martinberlin/epdiy-hardware-versions/versions/v7-raw-34/3dmodels/FH34SRJ-8S-0.5SH_50.step

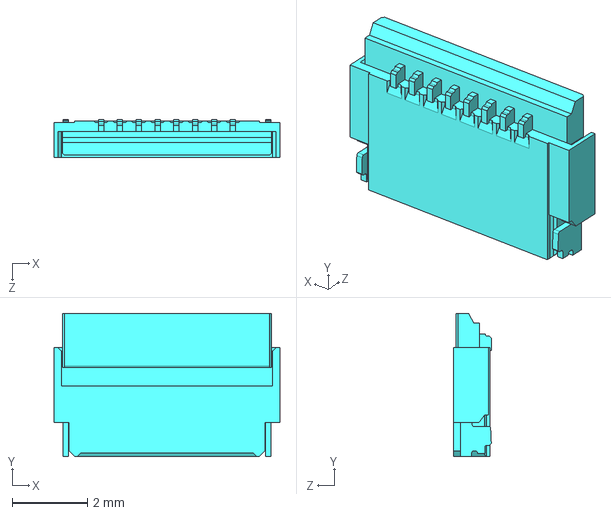
[picture p26: CAD file, 2025-05-24]
versions/v7-raw-34/3dmodels/FH34SRJ-8S-0.5SH_50.step
6.00 x 3.80 x 1.00 mm
