martinberlin/epdiy-hardware-versions/versions/v7-raw-34/kicad-libraries/3d/ESP32-S2-WROOM.STEP

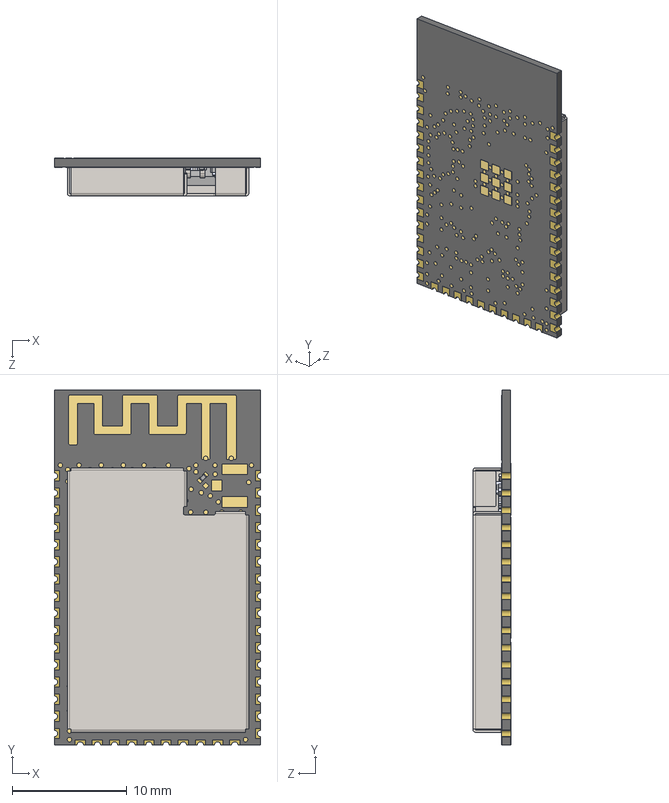
[picture p27: CAD file, 2025-05-24]
versions/v7-raw-34/kicad-libraries/3d/ESP32-S2-WROOM.STEP
18.0 x 31.0 x 3.30 mm
ESP32-S2_20210301.STEP^ESP32-S2_20210301.STEP_Submodel-QFN56_0P4_7_part_DesignRootModel_PCB_ESP32-S2-WROOM_V1(2)_PCB_ESP32-S2-WROOM_V1
R0201_20210301.STEP^R0201_20210301.STEP_Submodel-R0201_part_DesignRootModel_PCB_ESP32-S2-WROOM_V1(2)_PCB_ESP32-S2-WROOM_V1 x 7
trace_1^Submodel-MINI_ANT_TYPEB_1501846164_part_DesignRootModel_PCB_ESP32-S2-WROOM_V1(2)_PCB_ESP32-S2-WROOM_V1
C0201_20210301.STEP^C0201_20210301.STEP_Submodel-C0201_part_DesignRootModel_PCB_ESP32-S2-WROOM_V1(2)_PCB_ESP32-S2-WROOM_V1 x 15
DFN1006.STEP^DFN1006.STEP_Submodel-SOD882_part_DesignRootModel_PCB_ESP32-S2-WROOM_V1(2)_PCB_ESP32-S2-WROOM_V1
R0201_20210301.STEP^R0201_20210301.STEP_Submodel-R0201A_part_DesignRootModel_PCB_ESP32-S2-WROOM_V1(2)_PCB_ESP32-S2-WROOM_V1
L0201_20210301.STEP^L0201_20210301.STEP_Submodel-L0201_part_DesignRootModel_PCB_ESP32-S2-WROOM_V1(2)_PCB_ESP32-S2-WROOM_V1 x 2
C0402_20210301.STEP^C0402_20210301.STEP_Submodel-C0402_part_DesignRootModel_PCB_ESP32-S2-WROOM_V1(2)_PCB_ESP32-S2-WROOM_V1
XTAL3225_20210301.STEP^XTAL3225_20210301.STEP_Submodel-3225_part_DesignRootModel_PCB_ESP32-S2-WROOM_V1(2)_PCB_ESP32-S2-WROOM_V1
SOIC8_208_20210301.STEP^SOIC8_208_20210301.STEP_Submodel-SOIC08-WN_part_DesignRootModel_PCB_ESP32-S2-WROOM_V1(2)_PCB_ESP32-S2-WROOM_V1
uid__4-16^DesignRootModel_PCB_ESP32-S2-WROOM_V1(2)_PCB_ESP32-S2-WROOM_V1
uid__4-17^DesignRootModel_PCB_ESP32-S2-WROOM_V1(2)_PCB_ESP32-S2-WROOM_V1
uid__4-18^DesignRootModel_PCB_ESP32-S2-WROOM_V1(2)_PCB_ESP32-S2-WROOM_V1
uid__4-19^DesignRootModel_PCB_ESP32-S2-WROOM_V1(2)_PCB_ESP32-S2-WROOM_V1
uid__4-20^DesignRootModel_PCB_ESP32-S2-WROOM_V1(2)_PCB_ESP32-S2-WROOM_V1
uid__4-21^DesignRootModel_PCB_ESP32-S2-WROOM_V1(2)_PCB_ESP32-S2-WROOM_V1
uid__4-22^DesignRootModel_PCB_ESP32-S2-WROOM_V1(2)_PCB_ESP32-S2-WROOM_V1
uid__4-23^DesignRootModel_PCB_ESP32-S2-WROOM_V1(2)_PCB_ESP32-S2-WROOM_V1
uid__4-24^DesignRootModel_PCB_ESP32-S2-WROOM_V1(2)_PCB_ESP32-S2-WROOM_V1
uid__4-25^DesignRootModel_PCB_ESP32-S2-WROOM_V1(2)_PCB_ESP32-S2-WROOM_V1
uid__4-26^DesignRootModel_PCB_ESP32-S2-WROOM_V1(2)_PCB_ESP32-S2-WROOM_V1
uid__4-27^DesignRootModel_PCB_ESP32-S2-WROOM_V1(2)_PCB_ESP32-S2-WROOM_V1
uid__4-28^DesignRootModel_PCB_ESP32-S2-WROOM_V1(2)_PCB_ESP32-S2-WROOM_V1
uid__4-29^DesignRootModel_PCB_ESP32-S2-WROOM_V1(2)_PCB_ESP32-S2-WROOM_V1
uid__4-30^DesignRootModel_PCB_ESP32-S2-WROOM_V1(2)_PCB_ESP32-S2-WROOM_V1
uid__4-31^DesignRootModel_PCB_ESP32-S2-WROOM_V1(2)_PCB_ESP32-S2-WROOM_V1
uid__4-32^DesignRootModel_PCB_ESP32-S2-WROOM_V1(2)_PCB_ESP32-S2-WROOM_V1
uid__4-33^DesignRootModel_PCB_ESP32-S2-WROOM_V1(2)_PCB_ESP32-S2-WROOM_V1
uid__4-34^DesignRootModel_PCB_ESP32-S2-WROOM_V1(2)_PCB_ESP32-S2-WROOM_V1
uid__4-35^DesignRootModel_PCB_ESP32-S2-WROOM_V1(2)_PCB_ESP32-S2-WROOM_V1
uid__4-37^DesignRootModel_PCB_ESP32-S2-WROOM_V1(2)_PCB_ESP32-S2-WROOM_V1
uid__4-38^DesignRootModel_PCB_ESP32-S2-WROOM_V1(2)_PCB_ESP32-S2-WROOM_V1
uid__4-39^DesignRootModel_PCB_ESP32-S2-WROOM_V1(2)_PCB_ESP32-S2-WROOM_V1
uid__4-40^DesignRootModel_PCB_ESP32-S2-WROOM_V1(2)_PCB_ESP32-S2-WROOM_V1
uid__4-41^DesignRootModel_PCB_ESP32-S2-WROOM_V1(2)_PCB_ESP32-S2-WROOM_V1
uid__4-42^DesignRootModel_PCB_ESP32-S2-WROOM_V1(2)_PCB_ESP32-S2-WROOM_V1
uid__4-43^DesignRootModel_PCB_ESP32-S2-WROOM_V1(2)_PCB_ESP32-S2-WROOM_V1
uid__4-44^DesignRootModel_PCB_ESP32-S2-WROOM_V1(2)_PCB_ESP32-S2-WROOM_V1
uid__4-45^DesignRootModel_PCB_ESP32-S2-WROOM_V1(2)_PCB_ESP32-S2-WROOM_V1
uid__4-46^DesignRootModel_PCB_ESP32-S2-WROOM_V1(2)_PCB_ESP32-S2-WROOM_V1
uid__4-47^DesignRootModel_PCB_ESP32-S2-WROOM_V1(2)_PCB_ESP32-S2-WROOM_V1
uid__4-48^DesignRootModel_PCB_ESP32-S2-WROOM_V1(2)_PCB_ESP32-S2-WROOM_V1
uid__4-49^DesignRootModel_PCB_ESP32-S2-WROOM_V1(2)_PCB_ESP32-S2-WROOM_V1
uid__4-50^DesignRootModel_PCB_ESP32-S2-WROOM_V1(2)_PCB_ESP32-S2-WROOM_V1
uid__4-51^DesignRootModel_PCB_ESP32-S2-WROOM_V1(2)_PCB_ESP32-S2-WROOM_V1
uid__4-52^DesignRootModel_PCB_ESP32-S2-WROOM_V1(2)_PCB_ESP32-S2-WROOM_V1
uid__4-53^DesignRootModel_PCB_ESP32-S2-WROOM_V1(2)_PCB_ESP32-S2-WROOM_V1
uid__4-54^DesignRootModel_PCB_ESP32-S2-WROOM_V1(2)_PCB_ESP32-S2-WROOM_V1
uid__4-56^DesignRootModel_PCB_ESP32-S2-WROOM_V1(2)_PCB_ESP32-S2-WROOM_V1
uid__4-57^DesignRootModel_PCB_ESP32-S2-WROOM_V1(2)_PCB_ESP32-S2-WROOM_V1
uid__4-58^DesignRootModel_PCB_ESP32-S2-WROOM_V1(2)_PCB_ESP32-S2-WROOM_V1
uid__4-59^DesignRootModel_PCB_ESP32-S2-WROOM_V1(2)_PCB_ESP32-S2-WROOM_V1
uid__4-60^DesignRootModel_PCB_ESP32-S2-WROOM_V1(2)_PCB_ESP32-S2-WROOM_V1
uid__4-61^DesignRootModel_PCB_ESP32-S2-WROOM_V1(2)_PCB_ESP32-S2-WROOM_V1
uid__4-62^DesignRootModel_PCB_ESP32-S2-WROOM_V1(2)_PCB_ESP32-S2-WROOM_V1
uid__4-63^DesignRootModel_PCB_ESP32-S2-WROOM_V1(2)_PCB_ESP32-S2-WROOM_V1
uid__4-64^DesignRootModel_PCB_ESP32-S2-WROOM_V1(2)_PCB_ESP32-S2-WROOM_V1
uid__4-65^DesignRootModel_PCB_ESP32-S2-WROOM_V1(2)_PCB_ESP32-S2-WROOM_V1
uid__4-66^DesignRootModel_PCB_ESP32-S2-WROOM_V1(2)_PCB_ESP32-S2-WROOM_V1
uid__4-67^DesignRootModel_PCB_ESP32-S2-WROOM_V1(2)_PCB_ESP32-S2-WROOM_V1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
