martinberlin/epdiy-hardware-versions/versions/v7-raw-34/3dmodels/THD2528-11SD-GF_microSD.step

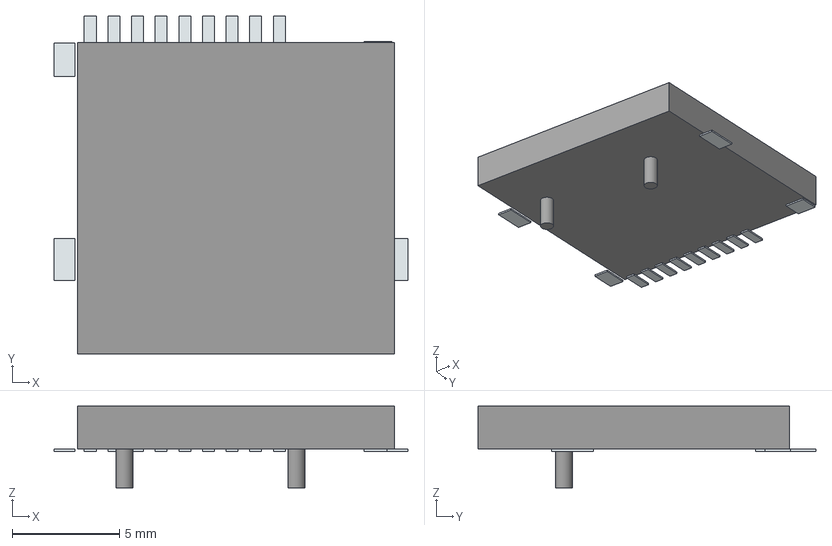
[picture p28: CAD file, 2025-05-24]
versions/v7-raw-34/3dmodels/THD2528-11SD-GF_microSD.step
16.5 x 15.7 x 3.80 mm
Pins
Lugs x 2
