martinberlin/epdiy-hardware-versions/versions/v7-raw-34/3dmodels/FH34SRJ-6S-0.5SH_99.step

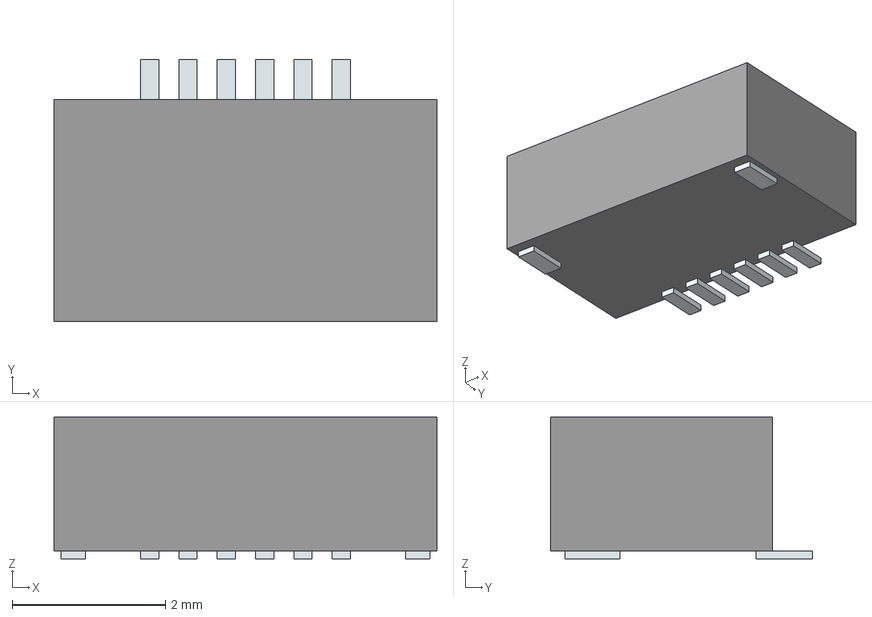
[picture p30: CAD file, 2025-05-24]
versions/v7-raw-34/3dmodels/FH34SRJ-6S-0.5SH_99.step
5.00 x 3.42 x 1.85 mm
Pins
