martinberlin/epdiy-hardware-versions/versions/v7-raw-34/kicad-libraries/3d/ESP32-S3-WROOM-1U.STEP

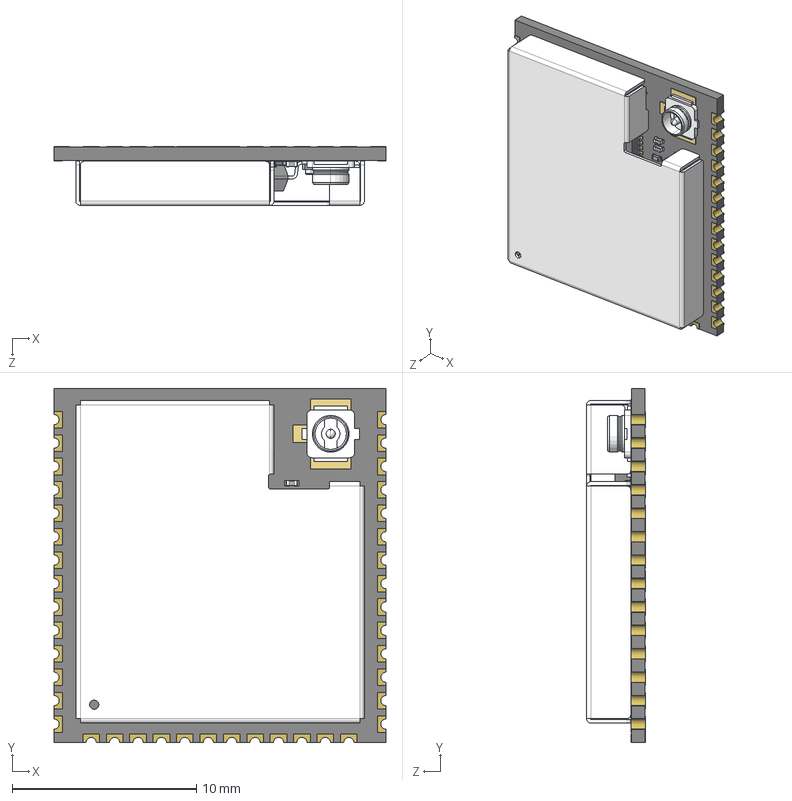
[picture p31: CAD file, 2025-05-24]
versions/v7-raw-34/kicad-libraries/3d/ESP32-S3-WROOM-1U.STEP
18.0 x 19.2 x 3.20 mm
R0201_20210301.STEP^R0201_20210301.STEP_Submodel-R0201_part_DesignRootModel_ESP32-S3-WROOM-1U(2)_ESP32-S3-WROOM-1U x 8
L0201_20210301.STEP^L0201_20210301.STEP_Submodel-L0201_part_DesignRootModel_ESP32-S3-WROOM-1U(2)_ESP32-S3-WROOM-1U x 2
C0201_20210301.STEP^C0201_20210301.STEP_Submodel-C0201_part_DesignRootModel_ESP32-S3-WROOM-1U(2)_ESP32-S3-WROOM-1U x 13
C0402_20210301.STEP^C0402_20210301.STEP_Submodel-C0402_part_DesignRootModel_ESP32-S3-WROOM-1U(2)_ESP32-S3-WROOM-1U
I-IPEX.STEP^I-IPEX.STEP_Submodel-IPEX_3P_part_DesignRootModel_ESP32-S3-WROOM-1U(2)_ESP32-S3-WROOM-1U
DFN1006.STEP^DFN1006.STEP_Submodel-SOD882_part_DesignRootModel_ESP32-S3-WROOM-1U(2)_ESP32-S3-WROOM-1U
SOP8_rev1_20210308.STEP^SOP8_rev1_20210308.STEP_Submodel-SOP8_1P27_6P6_part_DesignRootModel_ESP32-S3-WROOM-1U(2)_ESP32-S3-WROOM-1U
ESP32-S3_20210301.STEP^ESP32-S3_20210301.STEP_Submodel-QFN56_0P4_7_part_DesignRootModel_ESP32-S3-WROOM-1U(2)_ESP32-S3-WROOM-1U
XTAL3225_20210301.STEP^XTAL3225_20210301.STEP_Submodel-XTAL3225_part_DesignRootModel_ESP32-S3-WROOM-1U(2)_ESP32-S3-WROOM-1U
uid__4-111^DesignRootModel_ESP32-S3-WROOM-1U(2)_ESP32-S3-WROOM-1U
uid__4-112^DesignRootModel_ESP32-S3-WROOM-1U(2)_ESP32-S3-WROOM-1U
uid__4-113^DesignRootModel_ESP32-S3-WROOM-1U(2)_ESP32-S3-WROOM-1U
uid__4-130^DesignRootModel_ESP32-S3-WROOM-1U(2)_ESP32-S3-WROOM-1U
uid__4-131^DesignRootModel_ESP32-S3-WROOM-1U(2)_ESP32-S3-WROOM-1U
uid__4-132^DesignRootModel_ESP32-S3-WROOM-1U(2)_ESP32-S3-WROOM-1U
uid__4-148^DesignRootModel_ESP32-S3-WROOM-1U(2)_ESP32-S3-WROOM-1U
uid__4-149^DesignRootModel_ESP32-S3-WROOM-1U(2)_ESP32-S3-WROOM-1U
uid__4-150^DesignRootModel_ESP32-S3-WROOM-1U(2)_ESP32-S3-WROOM-1U
uid__1-253^DesignRootModel_ESP32-S3-WROOM-1U(2)_ESP32-S3-WROOM-1U
uid__1-254^DesignRootModel_ESP32-S3-WROOM-1U(2)_ESP32-S3-WROOM-1U
uid__1-256^DesignRootModel_ESP32-S3-WROOM-1U(2)_ESP32-S3-WROOM-1U
uid__1-257^DesignRootModel_ESP32-S3-WROOM-1U(2)_ESP32-S3-WROOM-1U
uid__1-266^DesignRootModel_ESP32-S3-WROOM-1U(2)_ESP32-S3-WROOM-1U
uid__1-269^DesignRootModel_ESP32-S3-WROOM-1U(2)_ESP32-S3-WROOM-1U
uid__1-270^DesignRootModel_ESP32-S3-WROOM-1U(2)_ESP32-S3-WROOM-1U
uid__1-271^DesignRootModel_ESP32-S3-WROOM-1U(2)_ESP32-S3-WROOM-1U
uid__1-272^DesignRootModel_ESP32-S3-WROOM-1U(2)_ESP32-S3-WROOM-1U
uid__1-273^DesignRootModel_ESP32-S3-WROOM-1U(2)_ESP32-S3-WROOM-1U
uid__1-274^DesignRootModel_ESP32-S3-WROOM-1U(2)_ESP32-S3-WROOM-1U
uid__1-275^DesignRootModel_ESP32-S3-WROOM-1U(2)_ESP32-S3-WROOM-1U
uid__1-276^DesignRootModel_ESP32-S3-WROOM-1U(2)_ESP32-S3-WROOM-1U
uid__1-277^DesignRootModel_ESP32-S3-WROOM-1U(2)_ESP32-S3-WROOM-1U
uid__1-280^DesignRootModel_ESP32-S3-WROOM-1U(2)_ESP32-S3-WROOM-1U
uid__1-292^DesignRootModel_ESP32-S3-WROOM-1U(2)_ESP32-S3-WROOM-1U
uid__1-293^DesignRootModel_ESP32-S3-WROOM-1U(2)_ESP32-S3-WROOM-1U
uid__1-297^DesignRootModel_ESP32-S3-WROOM-1U(2)_ESP32-S3-WROOM-1U
uid__1-300^DesignRootModel_ESP32-S3-WROOM-1U(2)_ESP32-S3-WROOM-1U
uid__1-301^DesignRootModel_ESP32-S3-WROOM-1U(2)_ESP32-S3-WROOM-1U
uid__1-302^DesignRootModel_ESP32-S3-WROOM-1U(2)_ESP32-S3-WROOM-1U
uid__1-303^DesignRootModel_ESP32-S3-WROOM-1U(2)_ESP32-S3-WROOM-1U
uid__1-307^DesignRootModel_ESP32-S3-WROOM-1U(2)_ESP32-S3-WROOM-1U
uid__1-313^DesignRootModel_ESP32-S3-WROOM-1U(2)_ESP32-S3-WROOM-1U
uid__1-319^DesignRootModel_ESP32-S3-WROOM-1U(2)_ESP32-S3-WROOM-1U
uid__1-320^DesignRootModel_ESP32-S3-WROOM-1U(2)_ESP32-S3-WROOM-1U
uid__1-321^DesignRootModel_ESP32-S3-WROOM-1U(2)_ESP32-S3-WROOM-1U
uid__1-328^DesignRootModel_ESP32-S3-WROOM-1U(2)_ESP32-S3-WROOM-1U
uid__1-332^DesignRootModel_ESP32-S3-WROOM-1U(2)_ESP32-S3-WROOM-1U
uid__1-333^DesignRootModel_ESP32-S3-WROOM-1U(2)_ESP32-S3-WROOM-1U
uid__1-334^DesignRootModel_ESP32-S3-WROOM-1U(2)_ESP32-S3-WROOM-1U
uid__1-335^DesignRootModel_ESP32-S3-WROOM-1U(2)_ESP32-S3-WROOM-1U
uid__1-336^DesignRootModel_ESP32-S3-WROOM-1U(2)_ESP32-S3-WROOM-1U
uid__1-337^DesignRootModel_ESP32-S3-WROOM-1U(2)_ESP32-S3-WROOM-1U
uid__1-338^DesignRootModel_ESP32-S3-WROOM-1U(2)_ESP32-S3-WROOM-1U
uid__1-339^DesignRootModel_ESP32-S3-WROOM-1U(2)_ESP32-S3-WROOM-1U
uid__1-340^DesignRootModel_ESP32-S3-WROOM-1U(2)_ESP32-S3-WROOM-1U
uid__1-341^DesignRootModel_ESP32-S3-WROOM-1U(2)_ESP32-S3-WROOM-1U
uid__1-342^DesignRootModel_ESP32-S3-WROOM-1U(2)_ESP32-S3-WROOM-1U
uid__1-343^DesignRootModel_ESP32-S3-WROOM-1U(2)_ESP32-S3-WROOM-1U
uid__1-344^DesignRootModel_ESP32-S3-WROOM-1U(2)_ESP32-S3-WROOM-1U
uid__1-345^DesignRootModel_ESP32-S3-WROOM-1U(2)_ESP32-S3-WROOM-1U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
