martinberlin/epdiy-hardware-versions/versions/v7-raw-34/3dmodels/L-40xx.STEP

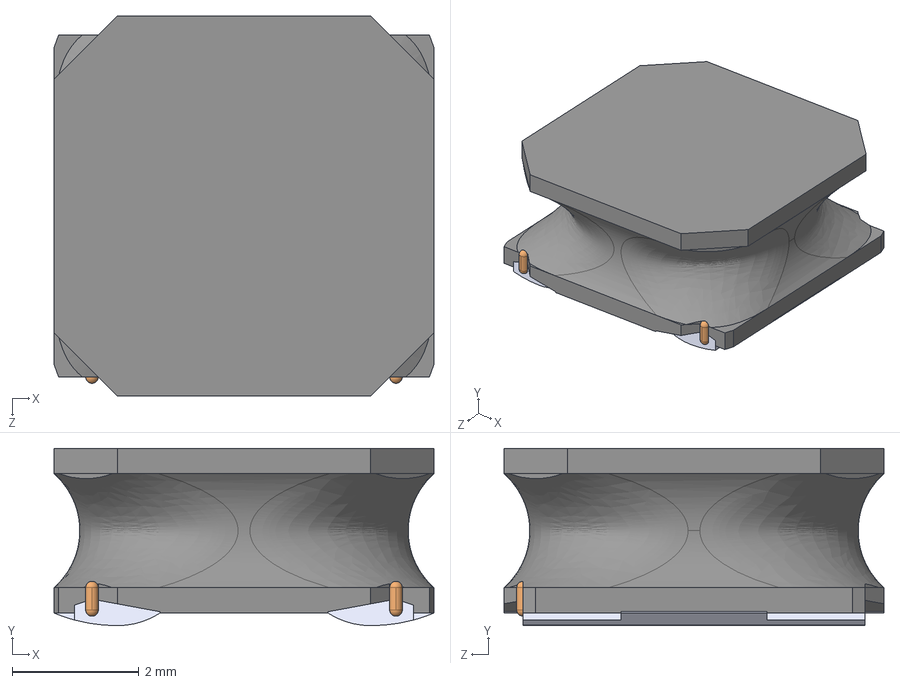
[picture p32: CAD file, 2025-05-24]
versions/v7-raw-34/3dmodels/L-40xx.STEP
6.00 x 2.80 x 6.00 mm
