martinberlin/epdiy-hardware-versions/versions/v7-raw-34/kicad-libraries/3d/ESP32-S2-MINI-1U.STEP

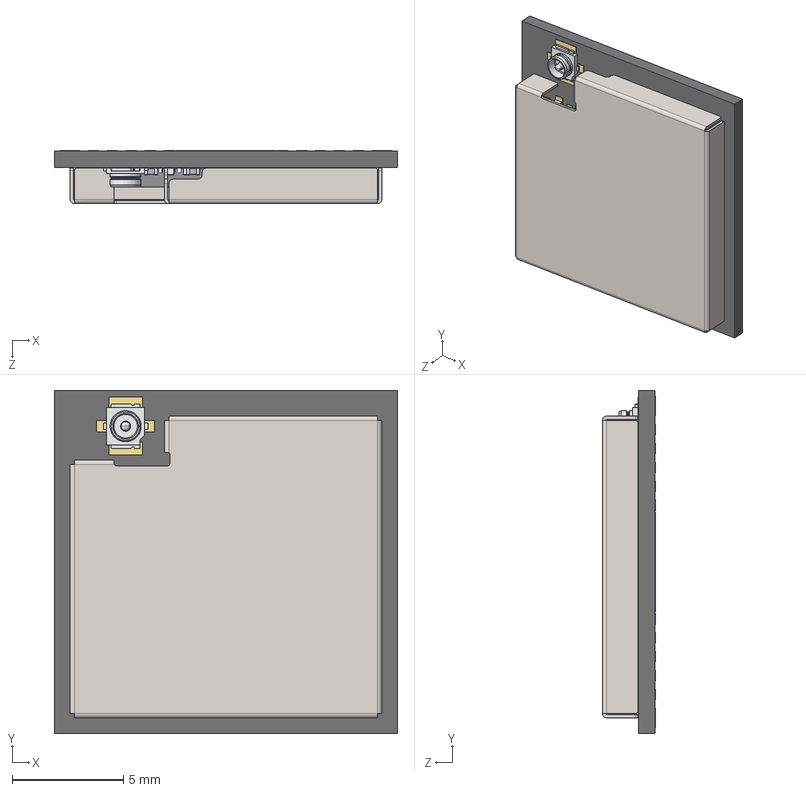
[picture p33: CAD file, 2025-05-24]
versions/v7-raw-34/kicad-libraries/3d/ESP32-S2-MINI-1U.STEP
15.4 x 15.4 x 2.40 mm
DFN1006.STEP^DFN1006.STEP_Submodel-SOD882_part_DesignRootModel_PCB_ESP32-S2-MINI-1U_V1(2)_PCB_ESP32-S2-MINI-1U_V1
ipx3.STEP^ipx3.STEP_Submodel-IPEX_4P_part_DesignRootModel_PCB_ESP32-S2-MINI-1U_V1(2)_PCB_ESP32-S2-MINI-1U_V1
C0201_20210301.STEP^C0201_20210301.STEP_Submodel-C0201_part_DesignRootModel_PCB_ESP32-S2-MINI-1U_V1(2)_PCB_ESP32-S2-MINI-1U_V1 x 15
R0201_20210301.STEP^R0201_20210301.STEP_Submodel-R0201_part_DesignRootModel_PCB_ESP32-S2-MINI-1U_V1(2)_PCB_ESP32-S2-MINI-1U_V1 x 3
XTAL3225_20210301.STEP^XTAL3225_20210301.STEP_Submodel-XTAL3225_part_DesignRootModel_PCB_ESP32-S2-MINI-1U_V1(2)_PCB_ESP32-S2-MINI-1U_V1
ESP32-S2_20210301.STEP^ESP32-S2_20210301.STEP_Submodel-QFN56_0P4_7_part_DesignRootModel_PCB_ESP32-S2-MINI-1U_V1(2)_PCB_ESP32-S2-MINI-1U_V1
L0201_20210301.STEP^L0201_20210301.STEP_Submodel-L0201_part_DesignRootModel_PCB_ESP32-S2-MINI-1U_V1(2)_PCB_ESP32-S2-MINI-1U_V1 x 2
C0402_20210301.STEP^C0402_20210301.STEP_Submodel-C0402_part_DesignRootModel_PCB_ESP32-S2-MINI-1U_V1(2)_PCB_ESP32-S2-MINI-1U_V1
uid__4^DesignRootModel_PCB_ESP32-S2-MINI-1U_V1(2)_PCB_ESP32-S2-MINI-1U_V1
uid__4-0^DesignRootModel_PCB_ESP32-S2-MINI-1U_V1(2)_PCB_ESP32-S2-MINI-1U_V1
uid__4-1^DesignRootModel_PCB_ESP32-S2-MINI-1U_V1(2)_PCB_ESP32-S2-MINI-1U_V1
uid__4-2^DesignRootModel_PCB_ESP32-S2-MINI-1U_V1(2)_PCB_ESP32-S2-MINI-1U_V1
uid__4-3^DesignRootModel_PCB_ESP32-S2-MINI-1U_V1(2)_PCB_ESP32-S2-MINI-1U_V1
uid__4-4^DesignRootModel_PCB_ESP32-S2-MINI-1U_V1(2)_PCB_ESP32-S2-MINI-1U_V1
uid__4-5^DesignRootModel_PCB_ESP32-S2-MINI-1U_V1(2)_PCB_ESP32-S2-MINI-1U_V1
uid__4-6^DesignRootModel_PCB_ESP32-S2-MINI-1U_V1(2)_PCB_ESP32-S2-MINI-1U_V1
uid__4-7^DesignRootModel_PCB_ESP32-S2-MINI-1U_V1(2)_PCB_ESP32-S2-MINI-1U_V1
uid__4-8^DesignRootModel_PCB_ESP32-S2-MINI-1U_V1(2)_PCB_ESP32-S2-MINI-1U_V1
uid__4-9^DesignRootModel_PCB_ESP32-S2-MINI-1U_V1(2)_PCB_ESP32-S2-MINI-1U_V1
uid__4-10^DesignRootModel_PCB_ESP32-S2-MINI-1U_V1(2)_PCB_ESP32-S2-MINI-1U_V1
uid__4-11^DesignRootModel_PCB_ESP32-S2-MINI-1U_V1(2)_PCB_ESP32-S2-MINI-1U_V1
uid__4-12^DesignRootModel_PCB_ESP32-S2-MINI-1U_V1(2)_PCB_ESP32-S2-MINI-1U_V1
uid__4-13^DesignRootModel_PCB_ESP32-S2-MINI-1U_V1(2)_PCB_ESP32-S2-MINI-1U_V1
uid__4-14^DesignRootModel_PCB_ESP32-S2-MINI-1U_V1(2)_PCB_ESP32-S2-MINI-1U_V1
uid__4-15^DesignRootModel_PCB_ESP32-S2-MINI-1U_V1(2)_PCB_ESP32-S2-MINI-1U_V1
uid__4-35^DesignRootModel_PCB_ESP32-S2-MINI-1U_V1(2)_PCB_ESP32-S2-MINI-1U_V1
uid__4-36^DesignRootModel_PCB_ESP32-S2-MINI-1U_V1(2)_PCB_ESP32-S2-MINI-1U_V1
uid__4-45^DesignRootModel_PCB_ESP32-S2-MINI-1U_V1(2)_PCB_ESP32-S2-MINI-1U_V1
uid__4-46^DesignRootModel_PCB_ESP32-S2-MINI-1U_V1(2)_PCB_ESP32-S2-MINI-1U_V1
uid__4-53^DesignRootModel_PCB_ESP32-S2-MINI-1U_V1(2)_PCB_ESP32-S2-MINI-1U_V1
uid__4-54^DesignRootModel_PCB_ESP32-S2-MINI-1U_V1(2)_PCB_ESP32-S2-MINI-1U_V1
uid__4-67^DesignRootModel_PCB_ESP32-S2-MINI-1U_V1(2)_PCB_ESP32-S2-MINI-1U_V1
uid__4-68^DesignRootModel_PCB_ESP32-S2-MINI-1U_V1(2)_PCB_ESP32-S2-MINI-1U_V1
uid__4-71^DesignRootModel_PCB_ESP32-S2-MINI-1U_V1(2)_PCB_ESP32-S2-MINI-1U_V1
uid__4-72^DesignRootModel_PCB_ESP32-S2-MINI-1U_V1(2)_PCB_ESP32-S2-MINI-1U_V1
uid__4-73^DesignRootModel_PCB_ESP32-S2-MINI-1U_V1(2)_PCB_ESP32-S2-MINI-1U_V1
uid__4-76^DesignRootModel_PCB_ESP32-S2-MINI-1U_V1(2)_PCB_ESP32-S2-MINI-1U_V1
uid__4-77^DesignRootModel_PCB_ESP32-S2-MINI-1U_V1(2)_PCB_ESP32-S2-MINI-1U_V1
uid__4-85^DesignRootModel_PCB_ESP32-S2-MINI-1U_V1(2)_PCB_ESP32-S2-MINI-1U_V1
uid__4-86^DesignRootModel_PCB_ESP32-S2-MINI-1U_V1(2)_PCB_ESP32-S2-MINI-1U_V1
uid__4-92^DesignRootModel_PCB_ESP32-S2-MINI-1U_V1(2)_PCB_ESP32-S2-MINI-1U_V1
uid__4-93^DesignRootModel_PCB_ESP32-S2-MINI-1U_V1(2)_PCB_ESP32-S2-MINI-1U_V1
uid__4-94^DesignRootModel_PCB_ESP32-S2-MINI-1U_V1(2)_PCB_ESP32-S2-MINI-1U_V1
uid__4-98^DesignRootModel_PCB_ESP32-S2-MINI-1U_V1(2)_PCB_ESP32-S2-MINI-1U_V1
uid__4-99^DesignRootModel_PCB_ESP32-S2-MINI-1U_V1(2)_PCB_ESP32-S2-MINI-1U_V1
uid__4-110^DesignRootModel_PCB_ESP32-S2-MINI-1U_V1(2)_PCB_ESP32-S2-MINI-1U_V1
uid__4-111^DesignRootModel_PCB_ESP32-S2-MINI-1U_V1(2)_PCB_ESP32-S2-MINI-1U_V1
uid__4-122^DesignRootModel_PCB_ESP32-S2-MINI-1U_V1(2)_PCB_ESP32-S2-MINI-1U_V1
uid__4-123^DesignRootModel_PCB_ESP32-S2-MINI-1U_V1(2)_PCB_ESP32-S2-MINI-1U_V1
uid__4-124^DesignRootModel_PCB_ESP32-S2-MINI-1U_V1(2)_PCB_ESP32-S2-MINI-1U_V1
uid__4-127^DesignRootModel_PCB_ESP32-S2-MINI-1U_V1(2)_PCB_ESP32-S2-MINI-1U_V1
uid__4-128^DesignRootModel_PCB_ESP32-S2-MINI-1U_V1(2)_PCB_ESP32-S2-MINI-1U_V1
uid__4-135^DesignRootModel_PCB_ESP32-S2-MINI-1U_V1(2)_PCB_ESP32-S2-MINI-1U_V1
uid__4-146^DesignRootModel_PCB_ESP32-S2-MINI-1U_V1(2)_PCB_ESP32-S2-MINI-1U_V1
uid__4-156^DesignRootModel_PCB_ESP32-S2-MINI-1U_V1(2)_PCB_ESP32-S2-MINI-1U_V1
uid__4-157^DesignRootModel_PCB_ESP32-S2-MINI-1U_V1(2)_PCB_ESP32-S2-MINI-1U_V1
uid__4-162^DesignRootModel_PCB_ESP32-S2-MINI-1U_V1(2)_PCB_ESP32-S2-MINI-1U_V1
uid__4-163^DesignRootModel_PCB_ESP32-S2-MINI-1U_V1(2)_PCB_ESP32-S2-MINI-1U_V1
uid__4-175^DesignRootModel_PCB_ESP32-S2-MINI-1U_V1(2)_PCB_ESP32-S2-MINI-1U_V1
uid__4-190^DesignRootModel_PCB_ESP32-S2-MINI-1U_V1(2)_PCB_ESP32-S2-MINI-1U_V1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
