martinberlin/epdiy-hardware-versions/versions/v7-raw-34/3dmodels/IND_0S282MT_SNL.step

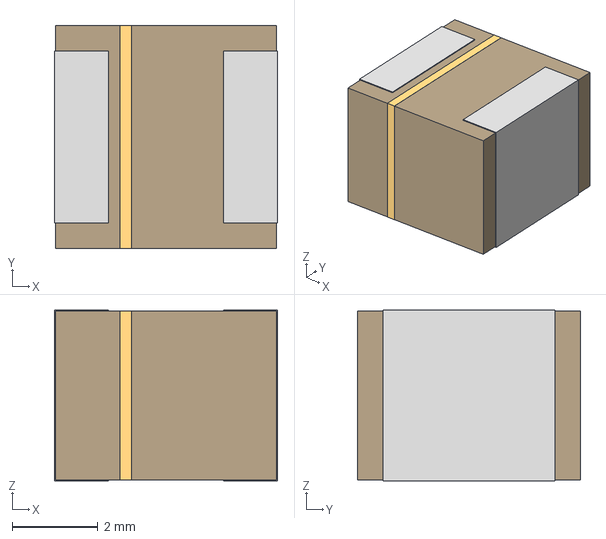
[picture p34: CAD file, 2025-05-24]
versions/v7-raw-34/3dmodels/IND_0S282MT_SNL.step
5.21 x 5.21 x 3.99 mm
