martinberlin/epdiy-hardware-versions/versions/v7-raw-34/3dmodels/X05A20H34G_EPD_connector.step

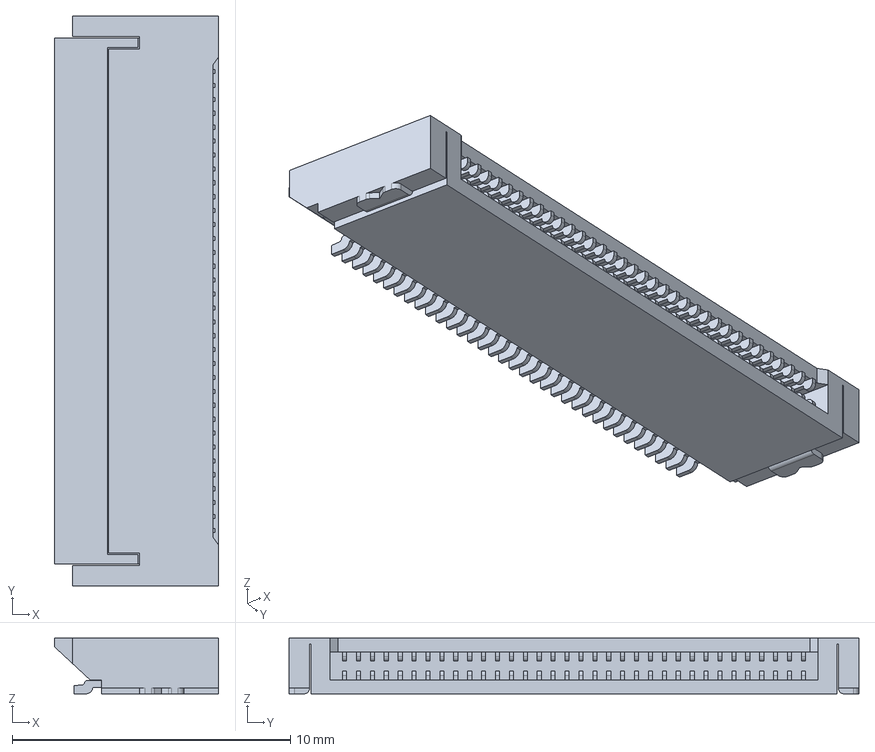
[picture p36: CAD file, 2025-05-24]
versions/v7-raw-34/3dmodels/X05A20H34G_EPD_connector.step
5.90 x 20.5 x 2.00 mm
