martinberlin/epdiy-hardware-versions/versions/v7-raw-34/3dmodels/Tactal Switch - SMD (5mmx 5mmx1.5mm).stp

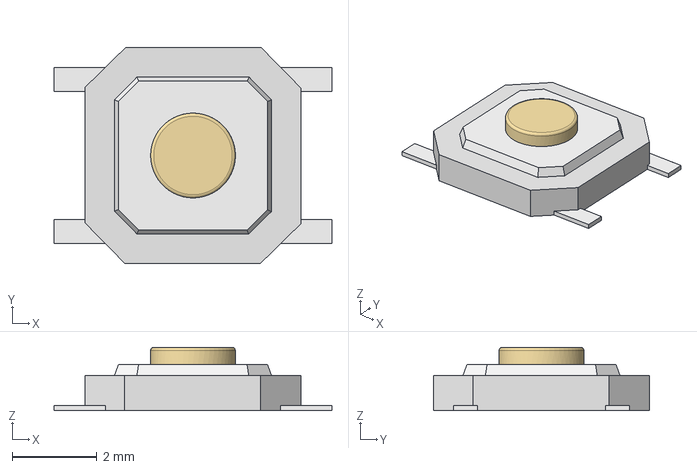
[picture p38: CAD file, 2025-05-24]
versions/v7-raw-34/3dmodels/Tactal Switch - SMD (5mmx 5mmx1.5mm).stp
6.58 x 5.10 x 1.50 mm
