martinberlin/epdiy-hardware-versions/versions/v7-raw-34/kicad-libraries/3d/ESP32-C3-MINI-1U.STEP

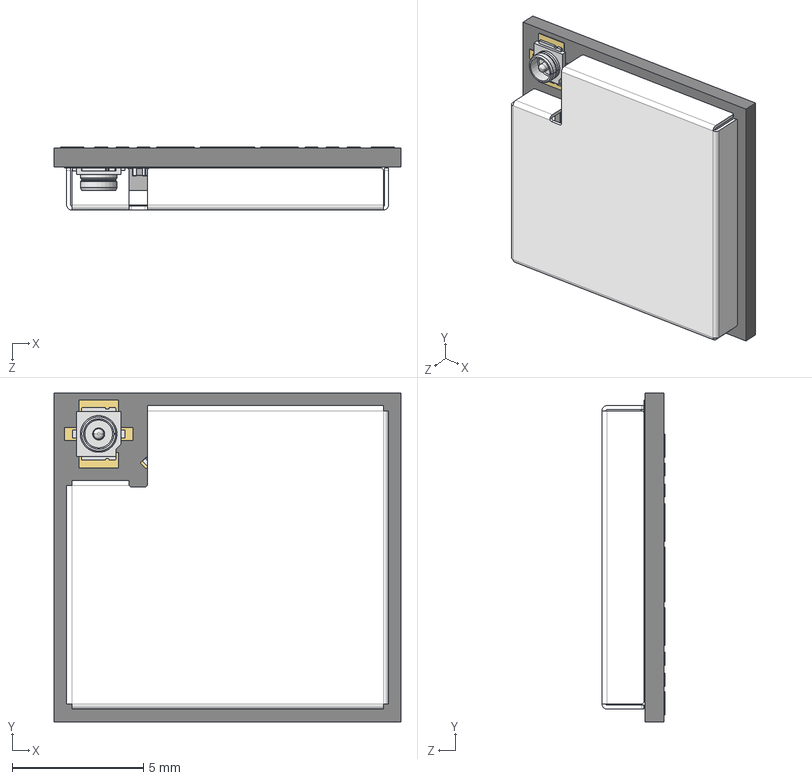
[picture p39: CAD file, 2025-05-24]
versions/v7-raw-34/kicad-libraries/3d/ESP32-C3-MINI-1U.STEP
13.2 x 12.5 x 2.40 mm
C0402_20210301.STEP^C0402_20210301.STEP_Submodel-C0402_part_DesignRootModel_PCB_ESP32-C3-MINI-1U_V2(2)_PCB_ESP32-C3-MINI-1U_V2
R0201_20210301.STEP^R0201_20210301.STEP_Submodel-R0201_part_DesignRootModel_PCB_ESP32-C3-MINI-1U_V2(2)_PCB_ESP32-C3-MINI-1U_V2 x 3
L0201_20210301.STEP^L0201_20210301.STEP_Submodel-L0201_part_DesignRootModel_PCB_ESP32-C3-MINI-1U_V2(2)_PCB_ESP32-C3-MINI-1U_V2 x 2
C0201_20210301.STEP^C0201_20210301.STEP_Submodel-C0201_part_DesignRootModel_PCB_ESP32-C3-MINI-1U_V2(2)_PCB_ESP32-C3-MINI-1U_V2 x 11
ESP32-C3_20210301.STEP^ESP32-C3_20210301.STEP_Submodel-QFN32_0P5_5_part_DesignRootModel_PCB_ESP32-C3-MINI-1U_V2(2)_PCB_ESP32-C3-MINI-1U_V2
DFN1006.STEP^DFN1006.STEP_Submodel-SOD882_part_DesignRootModel_PCB_ESP32-C3-MINI-1U_V2(2)_PCB_ESP32-C3-MINI-1U_V2
XTAL3225_20210301.STEP^XTAL3225_20210301.STEP_Submodel-XTAL3225_part_DesignRootModel_PCB_ESP32-C3-MINI-1U_V2(2)_PCB_ESP32-C3-MINI-1U_V2
ipx3.STEP^ipx3.STEP_Submodel-IPEX_4P_part_DesignRootModel_PCB_ESP32-C3-MINI-1U_V2(2)_PCB_ESP32-C3-MINI-1U_V2
uid__4^DesignRootModel_PCB_ESP32-C3-MINI-1U_V2(2)_PCB_ESP32-C3-MINI-1U_V2
uid__4-15^DesignRootModel_PCB_ESP32-C3-MINI-1U_V2(2)_PCB_ESP32-C3-MINI-1U_V2
uid__4-16^DesignRootModel_PCB_ESP32-C3-MINI-1U_V2(2)_PCB_ESP32-C3-MINI-1U_V2
uid__4-17^DesignRootModel_PCB_ESP32-C3-MINI-1U_V2(2)_PCB_ESP32-C3-MINI-1U_V2
uid__4-18^DesignRootModel_PCB_ESP32-C3-MINI-1U_V2(2)_PCB_ESP32-C3-MINI-1U_V2
uid__4-19^DesignRootModel_PCB_ESP32-C3-MINI-1U_V2(2)_PCB_ESP32-C3-MINI-1U_V2
uid__4-20^DesignRootModel_PCB_ESP32-C3-MINI-1U_V2(2)_PCB_ESP32-C3-MINI-1U_V2
uid__4-21^DesignRootModel_PCB_ESP32-C3-MINI-1U_V2(2)_PCB_ESP32-C3-MINI-1U_V2
uid__4-22^DesignRootModel_PCB_ESP32-C3-MINI-1U_V2(2)_PCB_ESP32-C3-MINI-1U_V2
uid__4-23^DesignRootModel_PCB_ESP32-C3-MINI-1U_V2(2)_PCB_ESP32-C3-MINI-1U_V2
uid__4-24^DesignRootModel_PCB_ESP32-C3-MINI-1U_V2(2)_PCB_ESP32-C3-MINI-1U_V2
uid__4-25^DesignRootModel_PCB_ESP32-C3-MINI-1U_V2(2)_PCB_ESP32-C3-MINI-1U_V2
uid__4-26^DesignRootModel_PCB_ESP32-C3-MINI-1U_V2(2)_PCB_ESP32-C3-MINI-1U_V2
uid__4-37^DesignRootModel_PCB_ESP32-C3-MINI-1U_V2(2)_PCB_ESP32-C3-MINI-1U_V2
uid__4-38^DesignRootModel_PCB_ESP32-C3-MINI-1U_V2(2)_PCB_ESP32-C3-MINI-1U_V2
uid__4-48^DesignRootModel_PCB_ESP32-C3-MINI-1U_V2(2)_PCB_ESP32-C3-MINI-1U_V2
uid__4-49^DesignRootModel_PCB_ESP32-C3-MINI-1U_V2(2)_PCB_ESP32-C3-MINI-1U_V2
uid__4-58^DesignRootModel_PCB_ESP32-C3-MINI-1U_V2(2)_PCB_ESP32-C3-MINI-1U_V2
uid__4-59^DesignRootModel_PCB_ESP32-C3-MINI-1U_V2(2)_PCB_ESP32-C3-MINI-1U_V2
uid__4-65^DesignRootModel_PCB_ESP32-C3-MINI-1U_V2(2)_PCB_ESP32-C3-MINI-1U_V2
uid__4-66^DesignRootModel_PCB_ESP32-C3-MINI-1U_V2(2)_PCB_ESP32-C3-MINI-1U_V2
uid__4-67^DesignRootModel_PCB_ESP32-C3-MINI-1U_V2(2)_PCB_ESP32-C3-MINI-1U_V2
uid__4-69^DesignRootModel_PCB_ESP32-C3-MINI-1U_V2(2)_PCB_ESP32-C3-MINI-1U_V2
uid__4-70^DesignRootModel_PCB_ESP32-C3-MINI-1U_V2(2)_PCB_ESP32-C3-MINI-1U_V2
uid__4-76^DesignRootModel_PCB_ESP32-C3-MINI-1U_V2(2)_PCB_ESP32-C3-MINI-1U_V2
uid__4-77^DesignRootModel_PCB_ESP32-C3-MINI-1U_V2(2)_PCB_ESP32-C3-MINI-1U_V2
uid__4-84^DesignRootModel_PCB_ESP32-C3-MINI-1U_V2(2)_PCB_ESP32-C3-MINI-1U_V2
uid__4-85^DesignRootModel_PCB_ESP32-C3-MINI-1U_V2(2)_PCB_ESP32-C3-MINI-1U_V2
uid__4-87^DesignRootModel_PCB_ESP32-C3-MINI-1U_V2(2)_PCB_ESP32-C3-MINI-1U_V2
uid__4-88^DesignRootModel_PCB_ESP32-C3-MINI-1U_V2(2)_PCB_ESP32-C3-MINI-1U_V2
uid__4-89^DesignRootModel_PCB_ESP32-C3-MINI-1U_V2(2)_PCB_ESP32-C3-MINI-1U_V2
uid__4-91^DesignRootModel_PCB_ESP32-C3-MINI-1U_V2(2)_PCB_ESP32-C3-MINI-1U_V2
uid__4-92^DesignRootModel_PCB_ESP32-C3-MINI-1U_V2(2)_PCB_ESP32-C3-MINI-1U_V2
uid__4-100^DesignRootModel_PCB_ESP32-C3-MINI-1U_V2(2)_PCB_ESP32-C3-MINI-1U_V2
uid__4-101^DesignRootModel_PCB_ESP32-C3-MINI-1U_V2(2)_PCB_ESP32-C3-MINI-1U_V2
uid__4-110^DesignRootModel_PCB_ESP32-C3-MINI-1U_V2(2)_PCB_ESP32-C3-MINI-1U_V2
uid__4-111^DesignRootModel_PCB_ESP32-C3-MINI-1U_V2(2)_PCB_ESP32-C3-MINI-1U_V2
uid__4-112^DesignRootModel_PCB_ESP32-C3-MINI-1U_V2(2)_PCB_ESP32-C3-MINI-1U_V2
uid__4-113^DesignRootModel_PCB_ESP32-C3-MINI-1U_V2(2)_PCB_ESP32-C3-MINI-1U_V2
uid__4-117^DesignRootModel_PCB_ESP32-C3-MINI-1U_V2(2)_PCB_ESP32-C3-MINI-1U_V2
uid__4-125^DesignRootModel_PCB_ESP32-C3-MINI-1U_V2(2)_PCB_ESP32-C3-MINI-1U_V2
uid__4-126^DesignRootModel_PCB_ESP32-C3-MINI-1U_V2(2)_PCB_ESP32-C3-MINI-1U_V2
uid__4-138^DesignRootModel_PCB_ESP32-C3-MINI-1U_V2(2)_PCB_ESP32-C3-MINI-1U_V2
uid__4-145^DesignRootModel_PCB_ESP32-C3-MINI-1U_V2(2)_PCB_ESP32-C3-MINI-1U_V2
uid__4-146^DesignRootModel_PCB_ESP32-C3-MINI-1U_V2(2)_PCB_ESP32-C3-MINI-1U_V2
uid__4-154^DesignRootModel_PCB_ESP32-C3-MINI-1U_V2(2)_PCB_ESP32-C3-MINI-1U_V2
uid__4-155^DesignRootModel_PCB_ESP32-C3-MINI-1U_V2(2)_PCB_ESP32-C3-MINI-1U_V2
uid__4-156^DesignRootModel_PCB_ESP32-C3-MINI-1U_V2(2)_PCB_ESP32-C3-MINI-1U_V2
uid__4-157^DesignRootModel_PCB_ESP32-C3-MINI-1U_V2(2)_PCB_ESP32-C3-MINI-1U_V2
uid__4-158^DesignRootModel_PCB_ESP32-C3-MINI-1U_V2(2)_PCB_ESP32-C3-MINI-1U_V2
uid__4-159^DesignRootModel_PCB_ESP32-C3-MINI-1U_V2(2)_PCB_ESP32-C3-MINI-1U_V2
uid__4-160^DesignRootModel_PCB_ESP32-C3-MINI-1U_V2(2)_PCB_ESP32-C3-MINI-1U_V2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
