martinberlin/epdiy-hardware-versions/versions/v7-raw-34/3dmodels/tps2113apwr.step

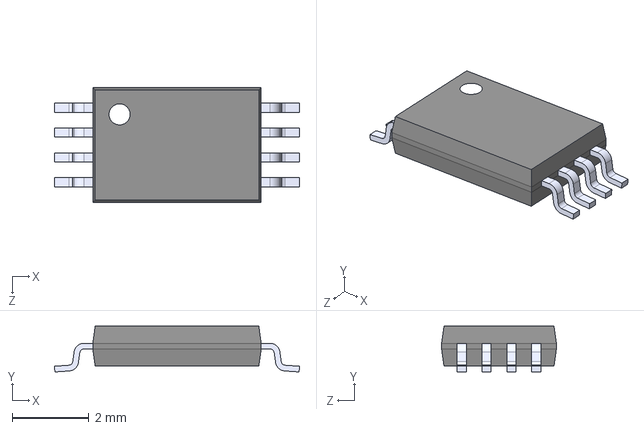
[picture p40: CAD file, 2025-05-24]
versions/v7-raw-34/3dmodels/tps2113apwr.step
6.40 x 1.20 x 3.00 mm
